ProgramHamza/antromorph/galeria/bocny_pohlad_na_AVK_krizenie_ligamentov_a_vedenie_ovladacichfilamentov.png

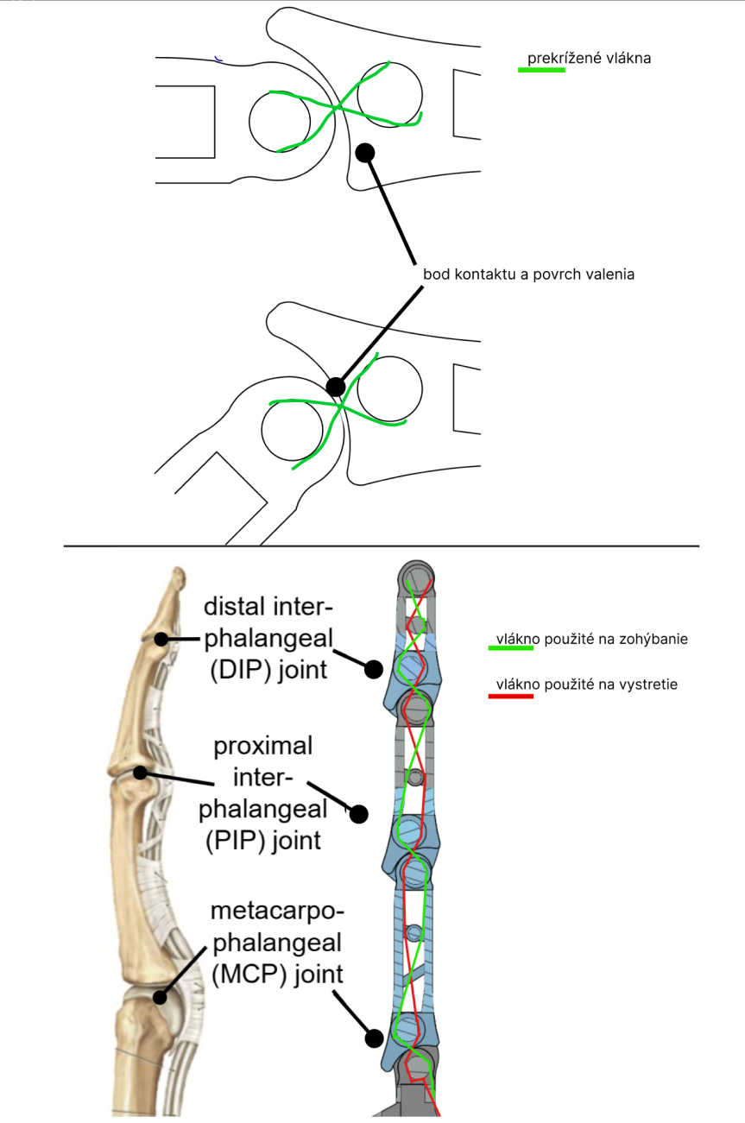
galeria/bocny_pohlad_na_AVK_krizenie_ligamentov_a_vedenie_ovladacichfilamentov.png
