ProgramHamza/antromorph/galeria/CAD_kresba_falangu.png

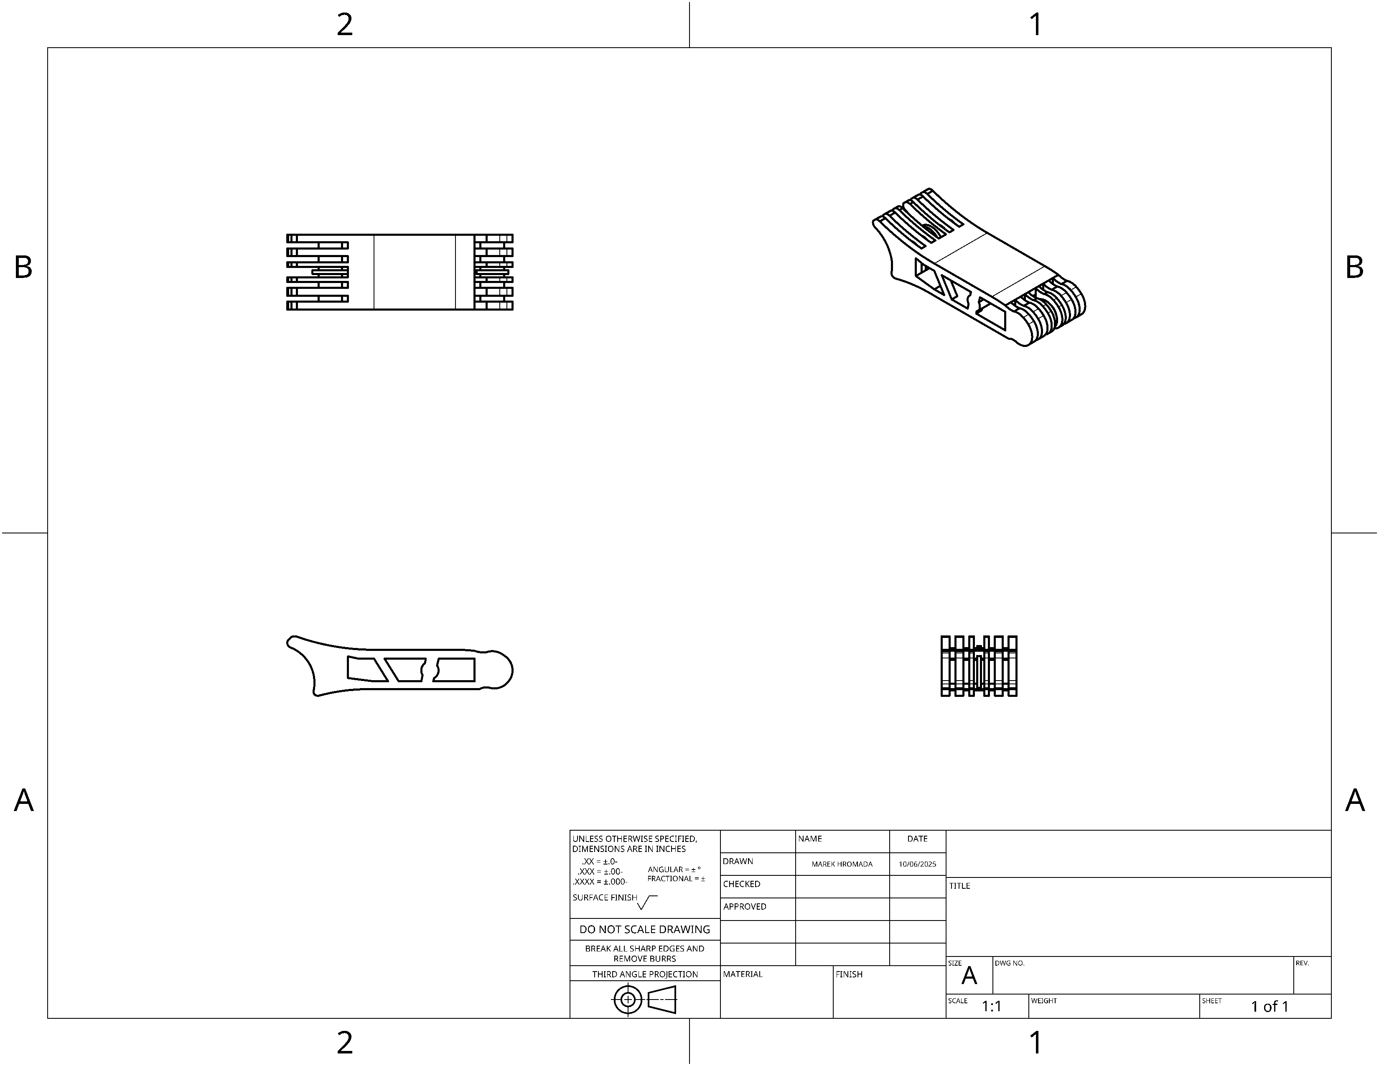
galeria/CAD_kresba_falangu.png
