ProgramHamza/antromorph/galeria/fotka_pocas_montaze_ruky.jpg

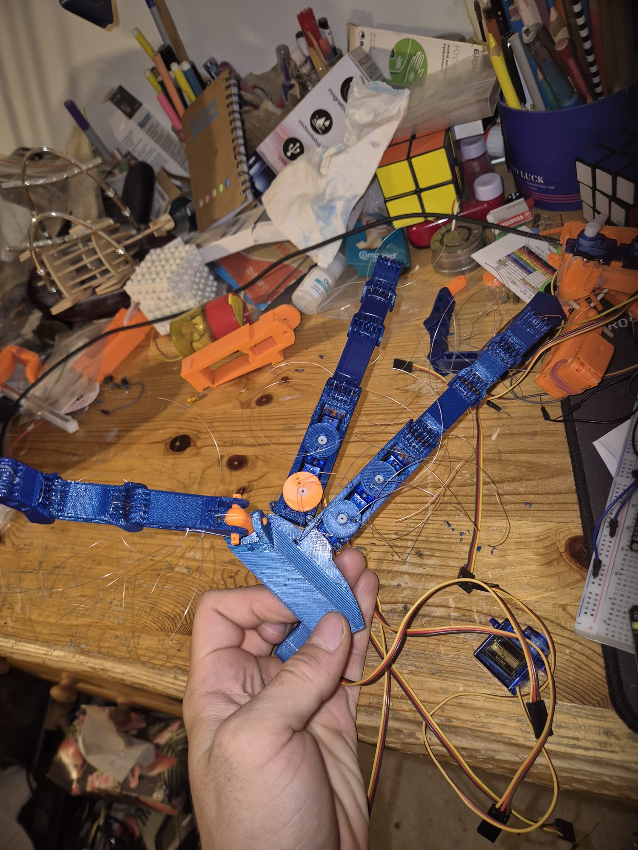
galeria/fotka_pocas_montaze_ruky.jpg
