ProgramHamza/antromorph/galeria/jeden AVK.jpg

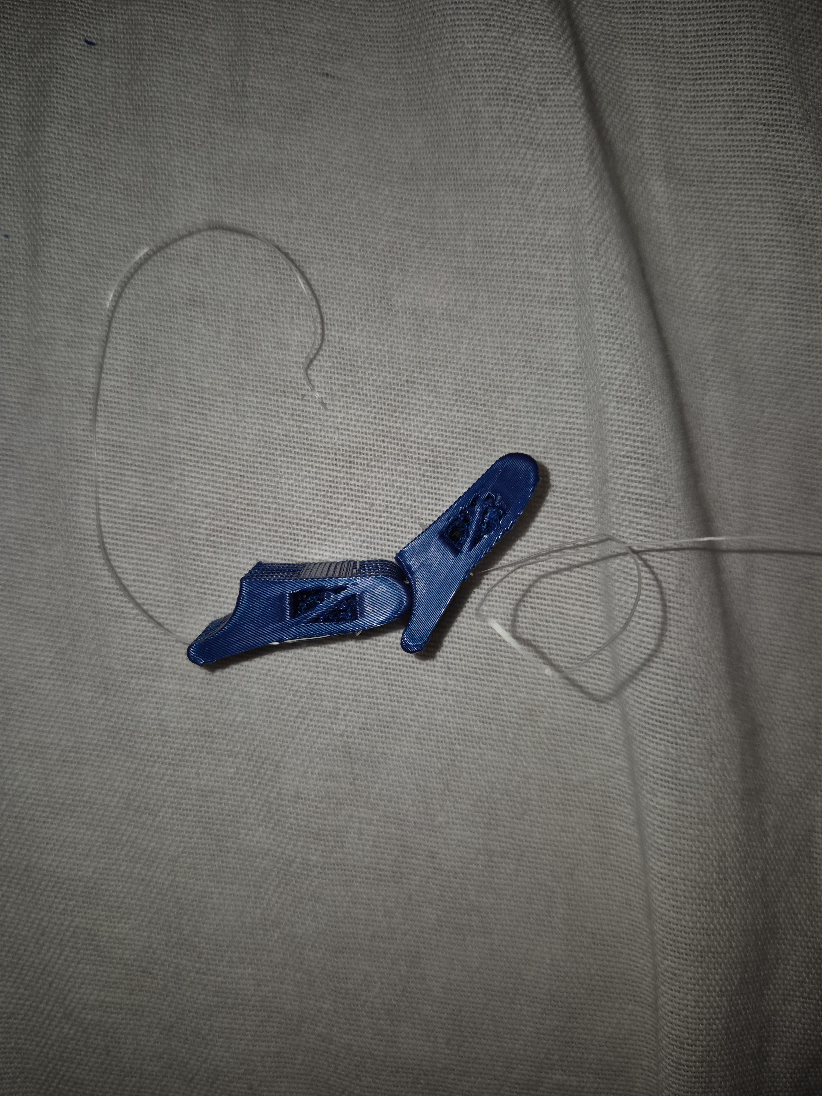
galeria/jeden AVK.jpg
