ProgramHamza/antromorph/galeria/von_misses_diagram_AVK.png

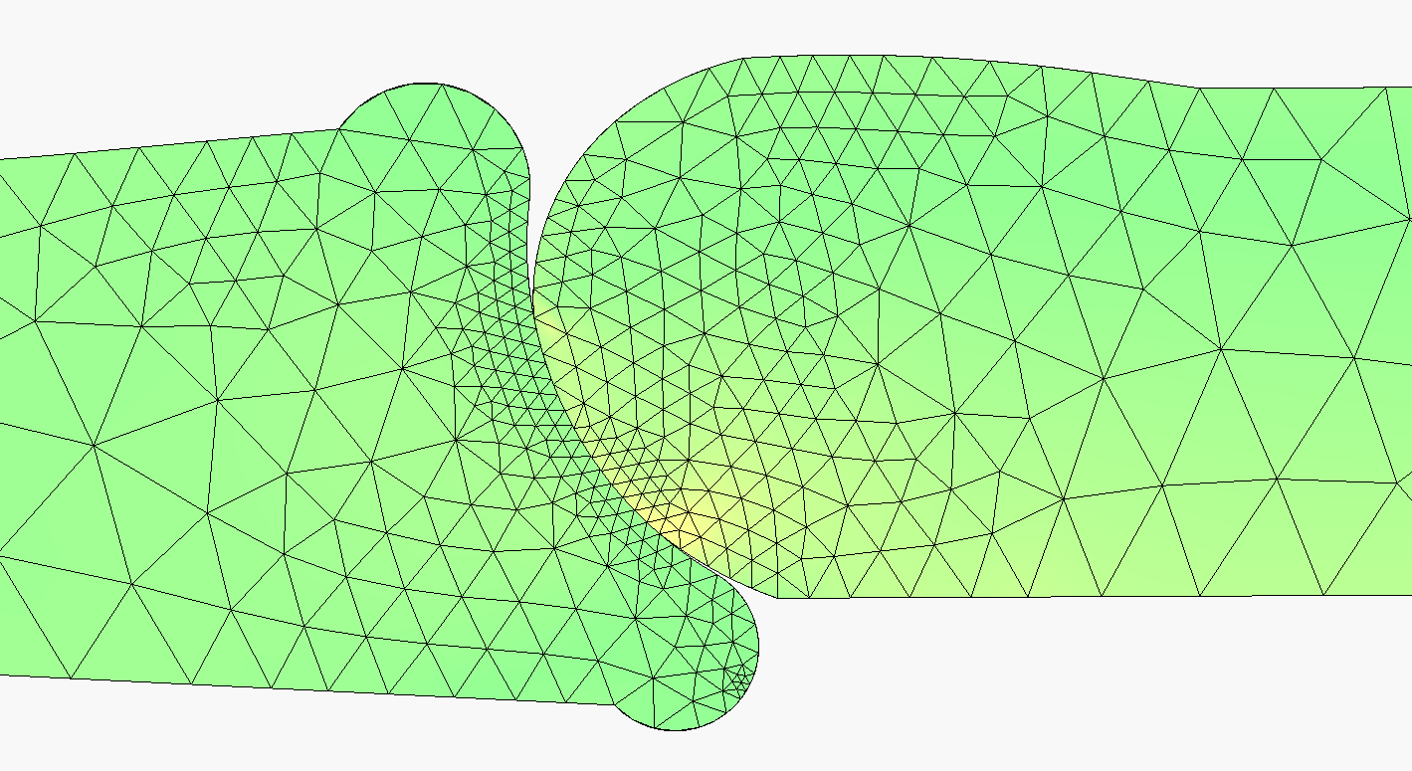
galeria/von_misses_diagram_AVK.png
