ProgramHamza/antromorph/galeria/zostavena_ruka_2.jpg

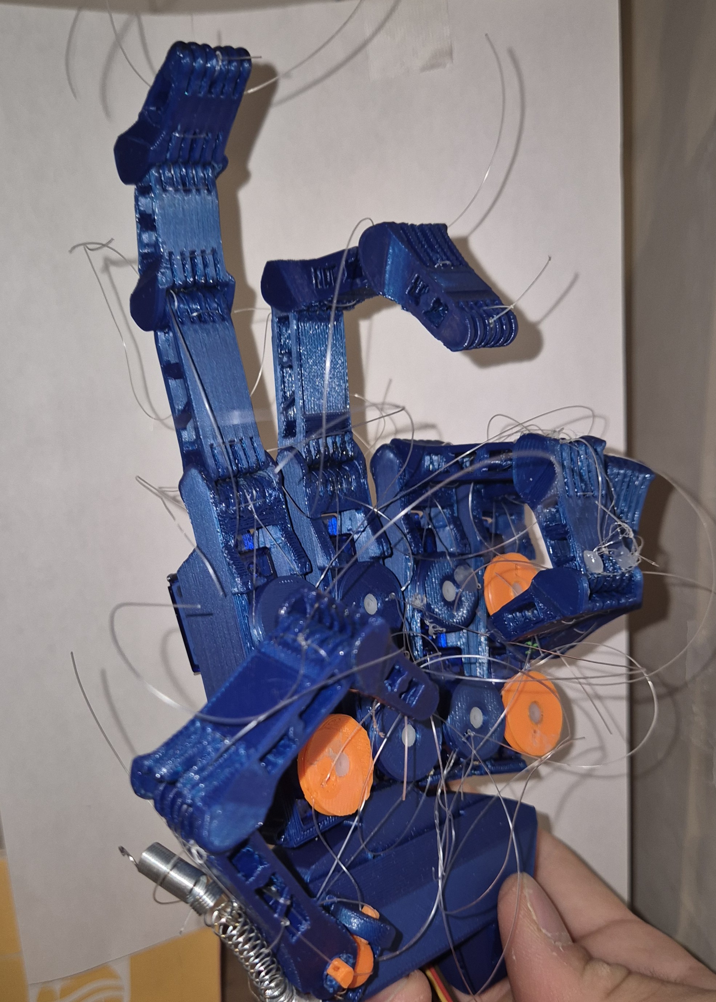
galeria/zostavena_ruka_2.jpg
