ProgramHamza/antromorph/galeria/zostaveny_prst.jpg

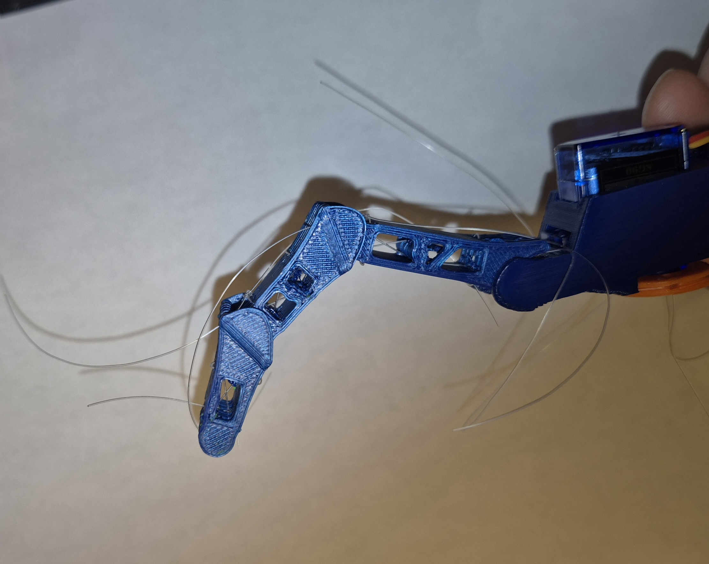
galeria/zostaveny_prst.jpg
