ProgramHamza/antromorph/na_stiahnutie_3d_modely/jednotlive_casti/prostrednik stred.obj

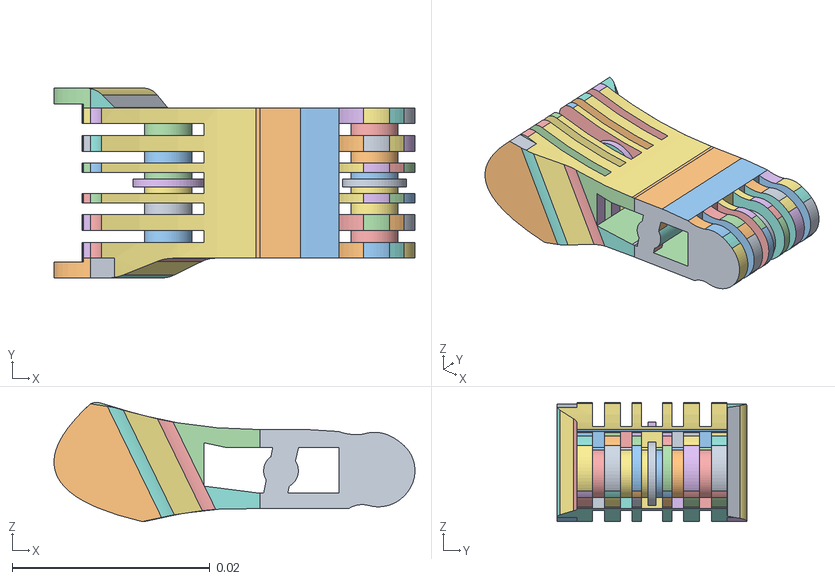
[picture p65: CAD file, 2025-11-04]
na_stiahnutie_3d_modely/jednotlive_casti/prostrednik stred.obj
0.0365 x 0.0192 x 0.012
