ProgramHamza/antromorph/na_stiahnutie_3d_modely/jednotlive_casti/drziak na serva vytlacit x3.obj

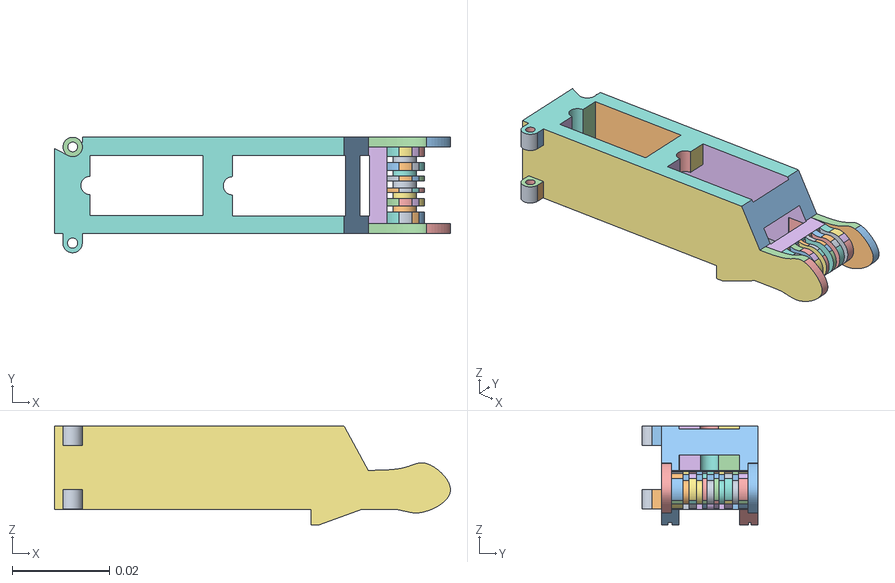
[picture p66: CAD file, 2025-11-04]
na_stiahnutie_3d_modely/jednotlive_casti/drziak na serva vytlacit x3.obj
0.0815 x 0.0238 x 0.0203
