ProgramHamza/antromorph/na_stiahnutie_3d_modely/jednotlive_casti/palec koncek.obj

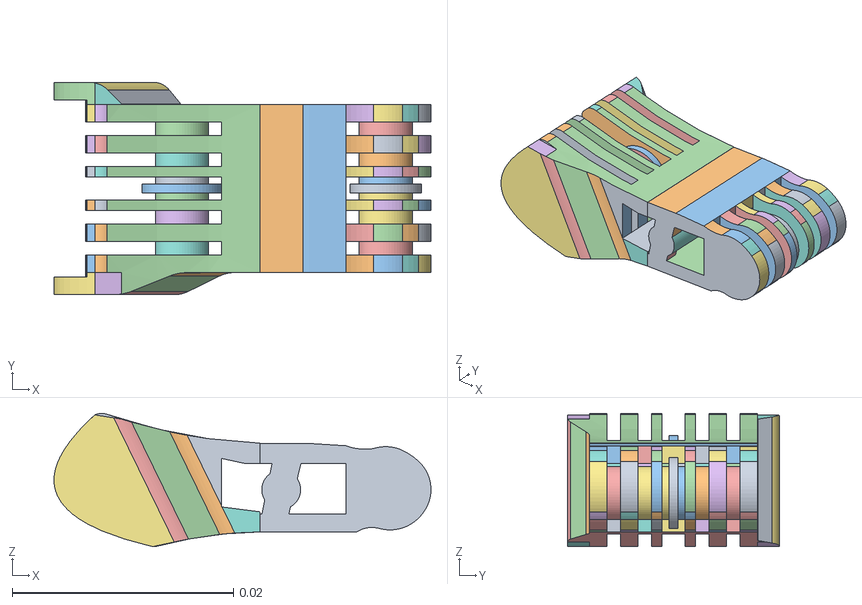
[picture p67: CAD file, 2025-11-04]
na_stiahnutie_3d_modely/jednotlive_casti/palec koncek.obj
0.0341 x 0.0192 x 0.012
